Lasertie/Open-ESP-board/Boitier/ILCboxv4.3mf

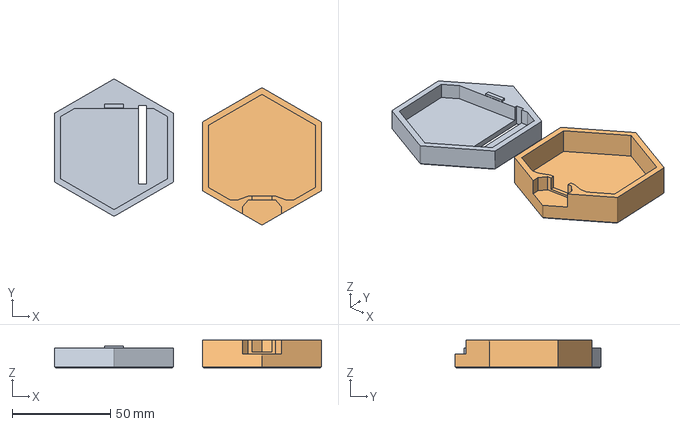
[picture p15: CAD file, 2025-04-07]
Boitier/ILCboxv4.3mf
135.9 x 74.3 x 14.0 mm
