Lasertie/Open-ESP-board/Boitier/ILCboxv3.3mf

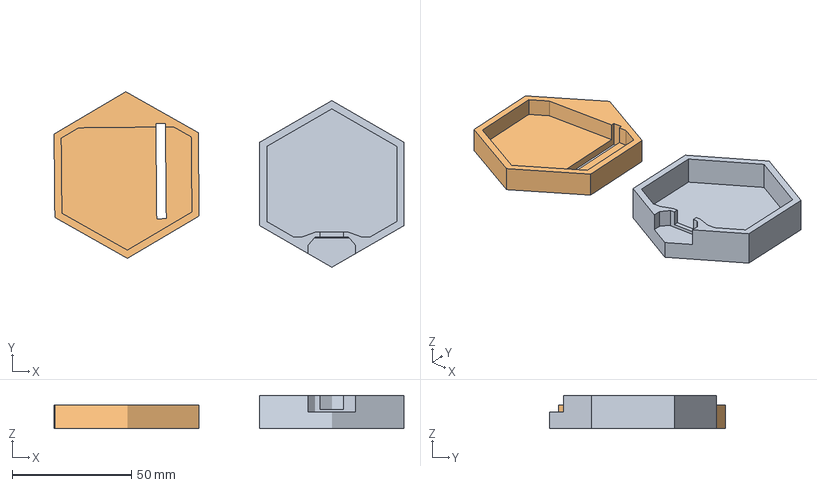
[picture p16: CAD file, 2025-04-07]
Boitier/ILCboxv3.3mf
147.0 x 73.7 x 14.0 mm
