Lasertie/Open-ESP-board/Boitier/ILCbox-bottom.3mf

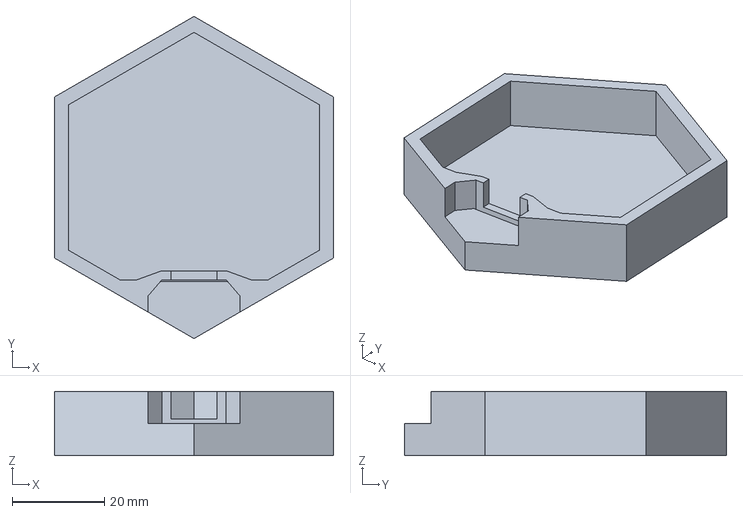
[picture p17: CAD file, 2025-04-07]
Boitier/ILCbox-bottom.3mf
60.6 x 70.0 x 14.0 mm
