Lasertie/Open-ESP-board/Boitier/IL/Radiateur.FCStd

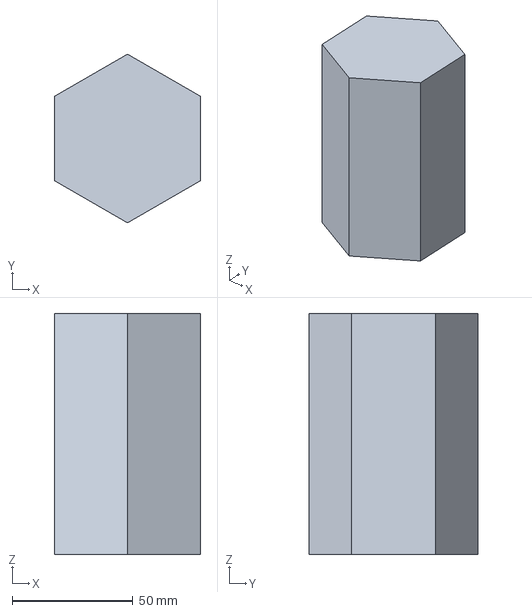
[picture p18: CAD file, 2025-04-07]
Boitier/IL/Radiateur.FCStd
60.6 x 70.0 x 100.0 mm
